perdidor/homebridge-diy-warmfloorcontroller/Photos/IMG_4534.JPG

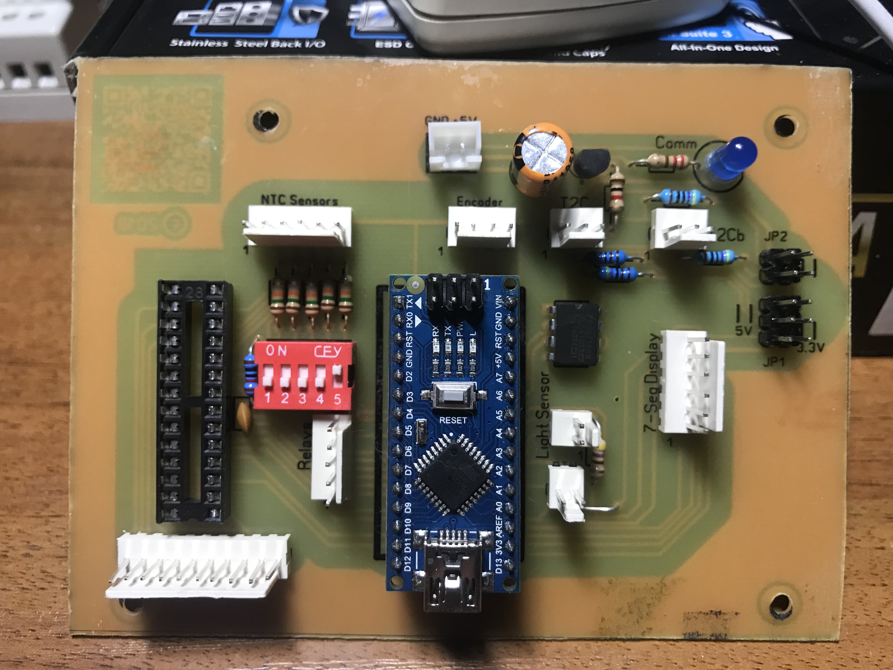
Photos/IMG_4534.JPG
