perdidor/homebridge-diy-warmfloorcontroller/Photos/IMG_4546.JPG

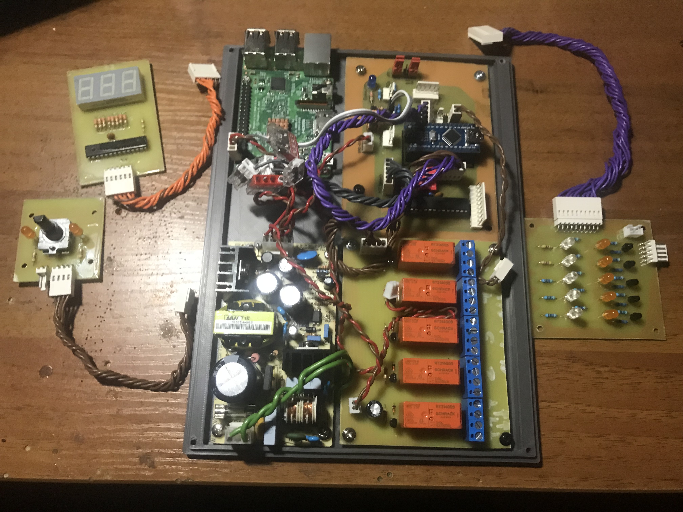
Photos/IMG_4546.JPG
