perdidor/homebridge-diy-warmfloorcontroller/Photos/IMG_4547.JPG

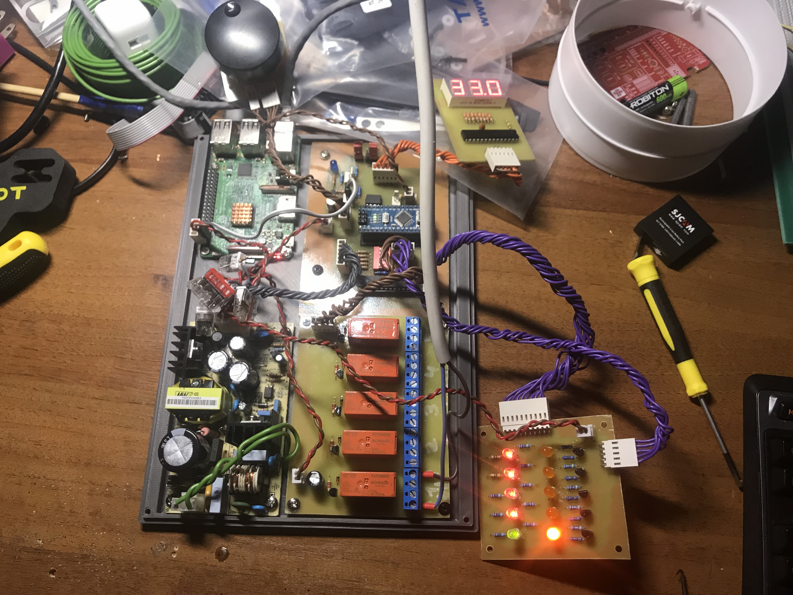
Photos/IMG_4547.JPG
